PrintersForAnts/AntHead/UserMods/Wristwatch-BMG/CAD/AntHead WW-BMG - Tension Arm Assembly.step

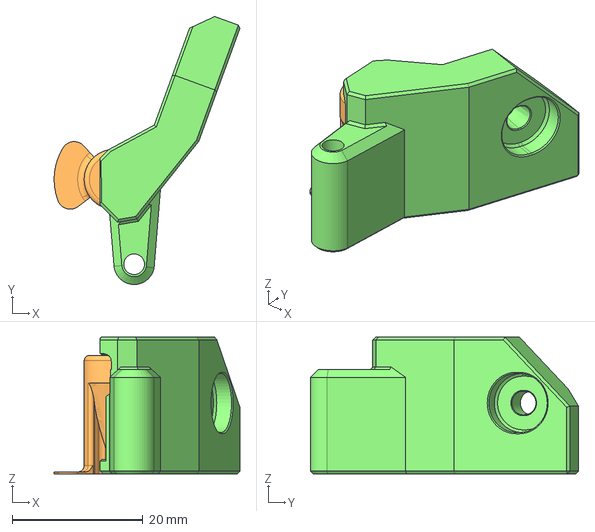
[picture p27: CAD file, 2025-04-11]
UserMods/Wristwatch-BMG/CAD/AntHead WW-BMG - Tension Arm Assembly.step
28.4 x 41.0 x 20.9 mm
WWBMG - Tension_Arm Support
AH WWBMG - Tension Arm
