PrintersForAnts/AntHead/UserMods/Papilio_Lite_Extruder_AntHead_Mod/STLs/AntHead_V43_Printed_Parts/LED_Logo_Assembly_x1.stl

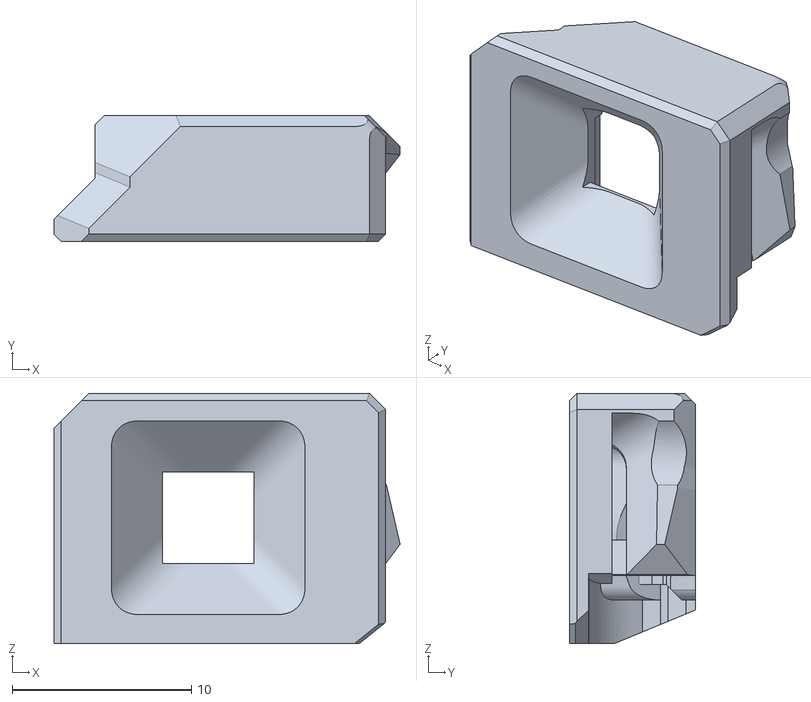
[picture p28: CAD file, 2025-02-15]
UserMods/Papilio_Lite_Extruder_AntHead_Mod/STLs/AntHead_V43_Printed_Parts/LED_Logo_Assembly_x1.stl
19.3 x 7.01 x 14.0
