PrintersForAnts/AntHead/Mini_AntHead/main_housing.stl

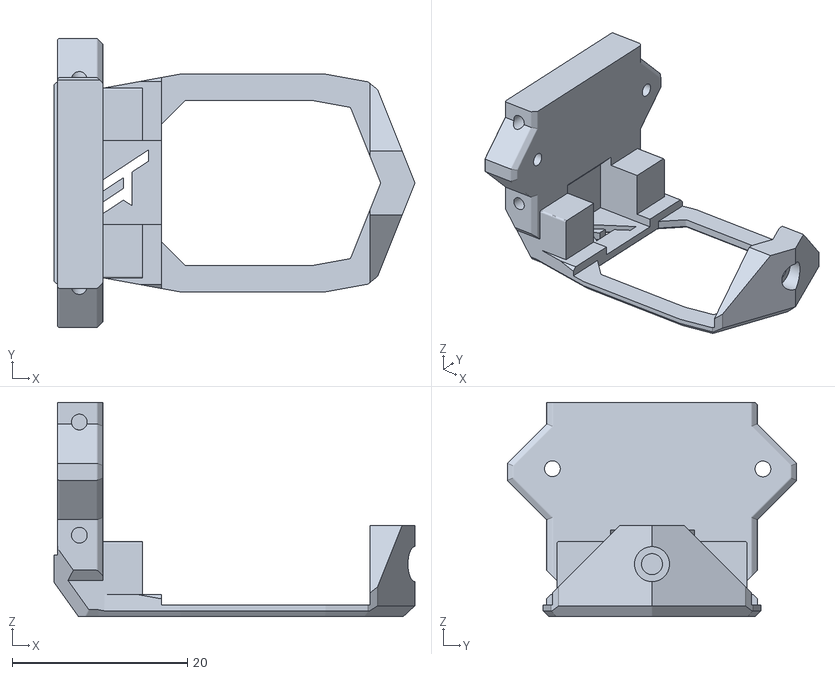
[picture p29: CAD file, 2025-01-11]
Mini_AntHead/main_housing.stl
41.2 x 33.0 x 24.4
