PrintersForAnts/AntHead/CAD/Base_CAD_Files/Anthead_Bowden.step

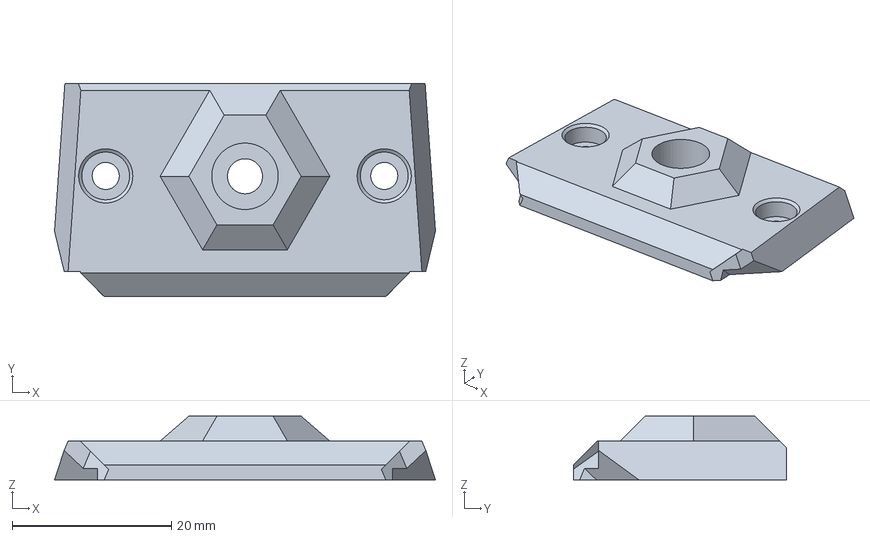
[picture p30: CAD file, 2025-11-22]
CAD/Base_CAD_Files/Anthead_Bowden.step
47.9 x 26.8 x 8.00 mm
