PrintersForAnts/AntHead/CAD/Extruders/NH36_Board_Cover.step

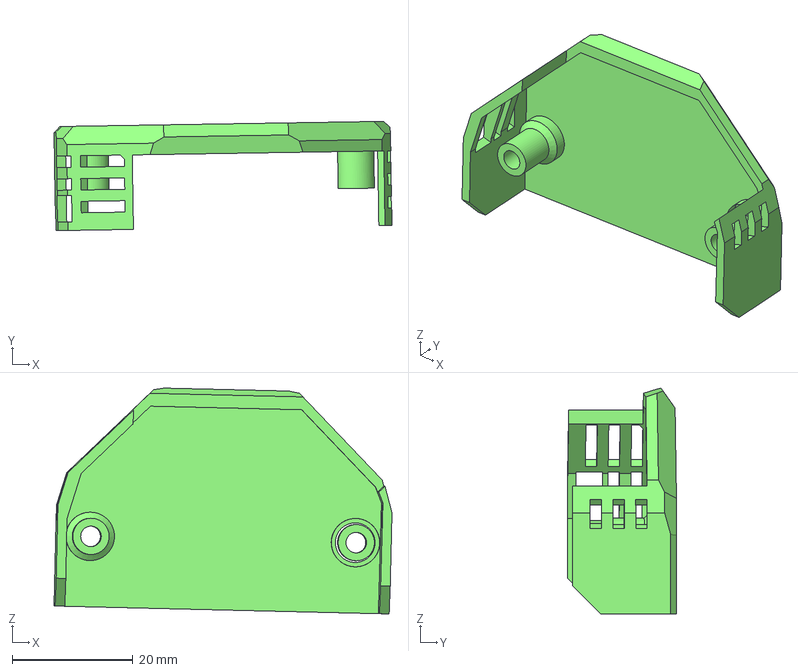
[picture p31: CAD file, 2025-07-28]
CAD/Extruders/NH36_Board_Cover.step
55.9 x 18.1 x 37.3 mm
