PrintersForAnts/AntHead/Mini_AntHead/[a]_logo_insert.stl

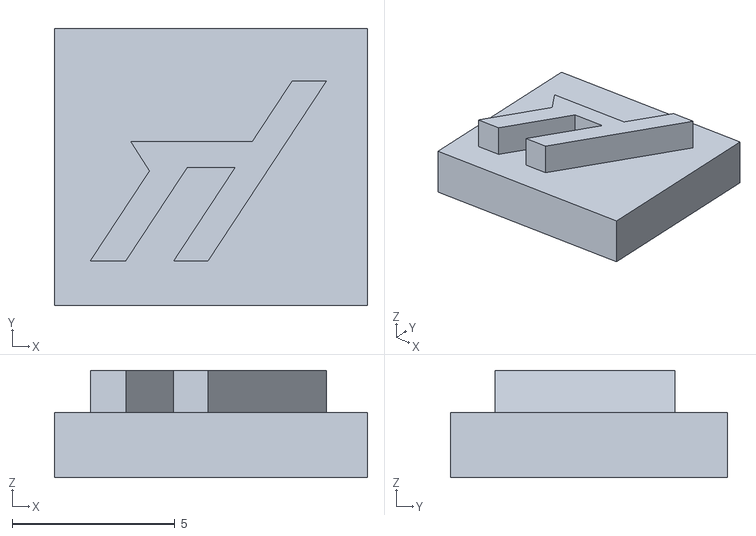
[picture p32: CAD file, 2025-01-11]
Mini_AntHead/[a]_logo_insert.stl
9.61 x 8.51 x 3.30
