PrintersForAnts/AntHead/STLs/2020_Carriage/beacon_carto_uhf_x1.stl

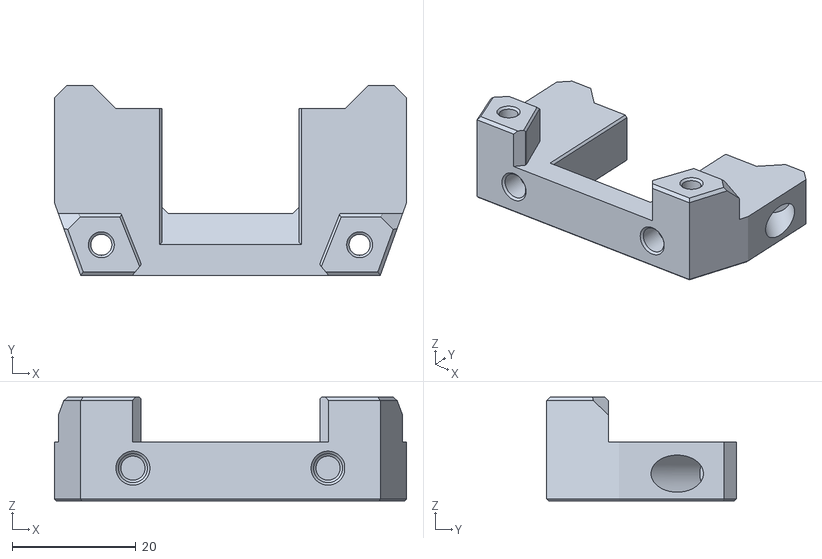
[picture p33: CAD file, 2025-08-02]
STLs/2020_Carriage/beacon_carto_uhf_x1.stl
57.0 x 30.7 x 16.8
