PrintersForAnts/AntHead/STLs/Ducts/HF/[a]_right_duct_hf_x1.stl

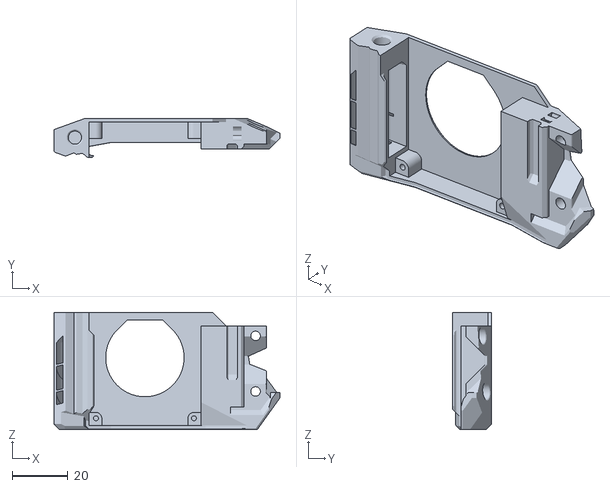
[picture p35: CAD file, 2025-07-28]
STLs/Ducts/HF/[a]_right_duct_hf_x1.stl
80.8 x 13.8 x 42.0
