PrintersForAnts/AntHead/STLs/Ducts/HF/Leaf_Cutter/[a]_left_duct_hf_hb92_lc_x1.stl

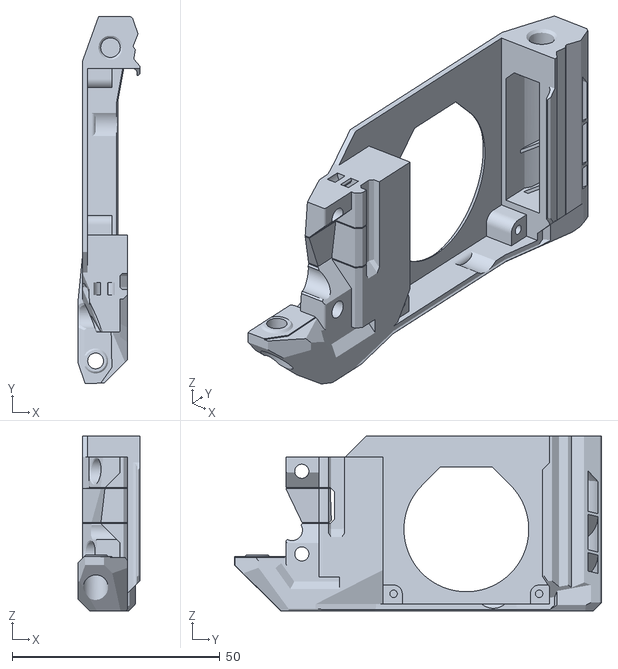
[picture p36: CAD file, 2025-07-28]
STLs/Ducts/HF/Leaf_Cutter/[a]_left_duct_hf_hb92_lc_x1.stl
14.8 x 88.2 x 42.0
