PrintersForAnts/AntHead/STLs/Ducts/SF/Leaf_Cutter/[a]_left_duct_lc_x1.stl

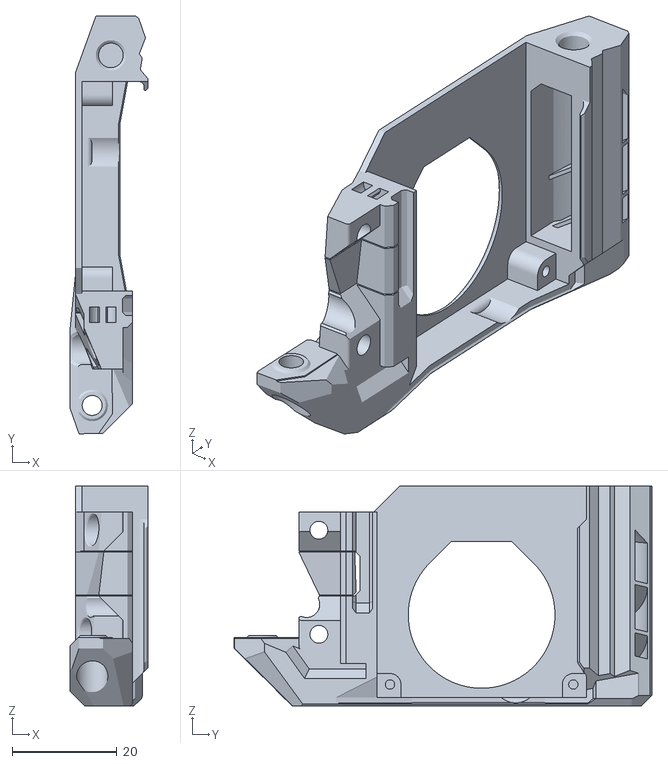
[picture p38: CAD file, 2025-07-28]
STLs/Ducts/SF/Leaf_Cutter/[a]_left_duct_lc_x1.stl
14.8 x 79.7 x 42.0
