PrintersForAnts/AntHead/STLs/Ducts/UHF/[a]_right_duct_uhf_x1.stl

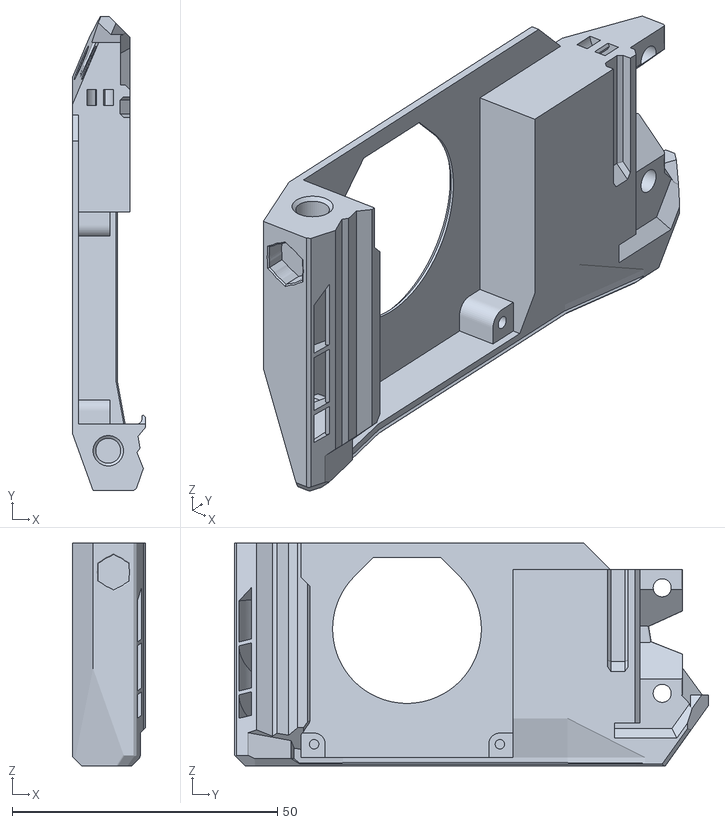
[picture p39: CAD file, 2025-07-28]
STLs/Ducts/UHF/[a]_right_duct_uhf_x1.stl
13.8 x 89.3 x 42.0
