PrintersForAnts/AntHead/STLs/Ducts/UHF/Leaf_Cutter/[a]_left_duct_uhf_lc_x1.stl

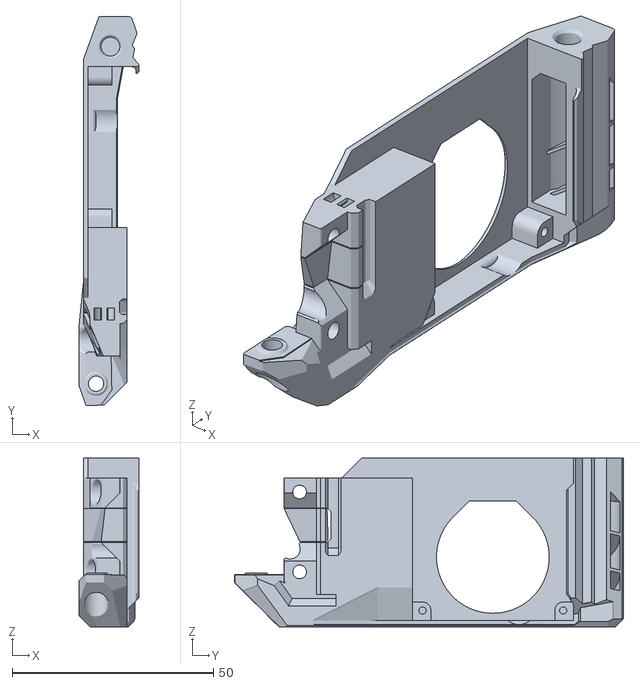
[picture p40: CAD file, 2025-07-28]
STLs/Ducts/UHF/Leaf_Cutter/[a]_left_duct_uhf_lc_x1.stl
14.8 x 96.7 x 42.0
