PrintersForAnts/AntHead/STLs/Extruders/BMG/BoardMounts/toolhead_board_mount_anthead_bmg_micron.stl

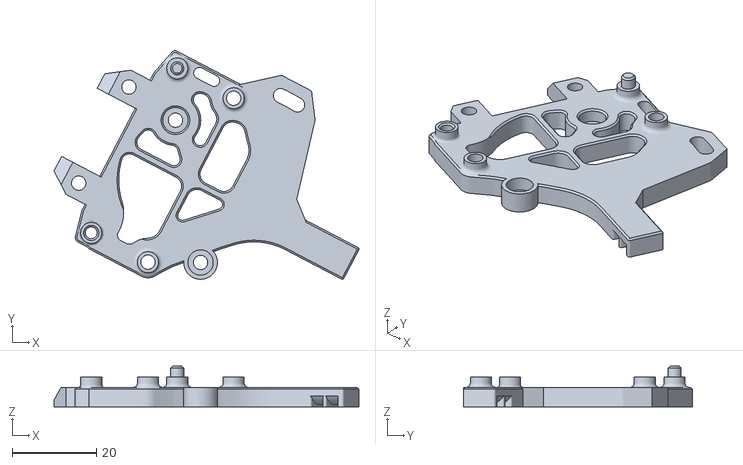
[picture p41: CAD file, 2025-07-28]
STLs/Extruders/BMG/BoardMounts/toolhead_board_mount_anthead_bmg_micron.stl
72.3 x 54.2 x 9.60
