PrintersForAnts/AntHead/STLs/Extruders/BMG/tensioner_arm_b_x1.stl

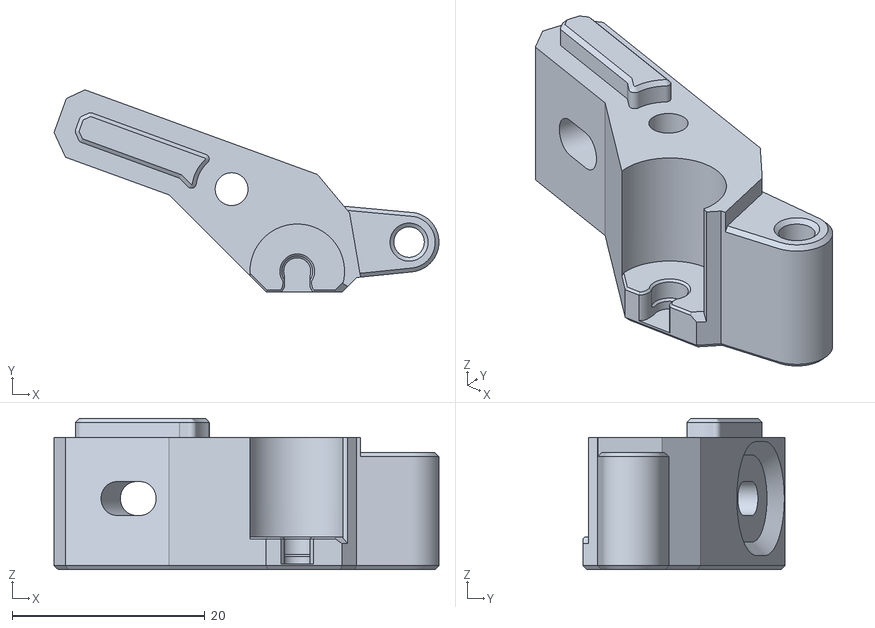
[picture p42: CAD file, 2024-10-09]
STLs/Extruders/BMG/tensioner_arm_b_x1.stl
39.9 x 21.0 x 15.7
