PrintersForAnts/AntHead/STLs/Extruders/G2/Board Mounts/toolhead_board_mount_anthead_G2_micron.stl

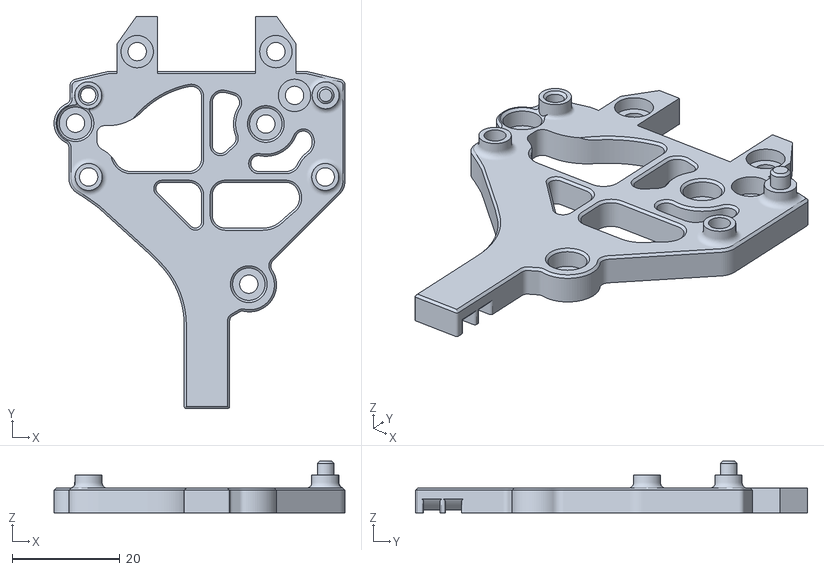
[picture p43: CAD file, 2025-07-28]
STLs/Extruders/G2/Board Mounts/toolhead_board_mount_anthead_G2_micron.stl
53.9 x 72.7 x 9.60
