PrintersForAnts/AntHead/STLs/Extruders/G2/pug_mount_a_x1.stl

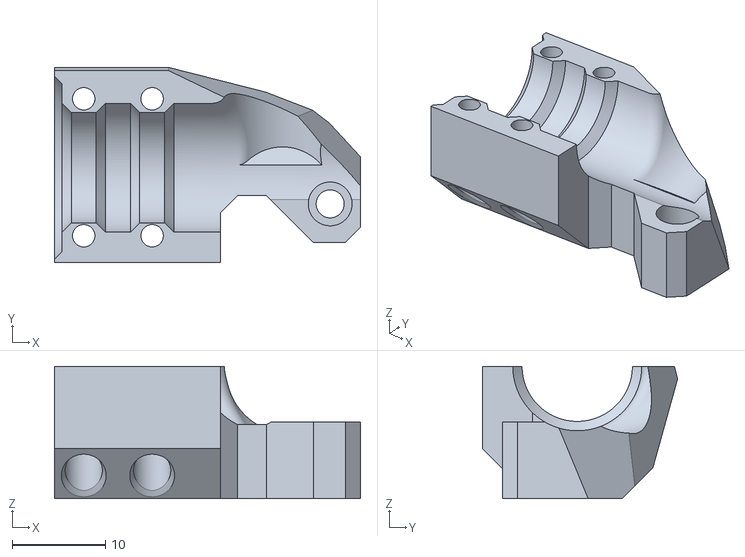
[picture p44: CAD file, 2025-10-02]
STLs/Extruders/G2/pug_mount_a_x1.stl
32.8 x 20.9 x 14.2
