PrintersForAnts/AntHead/STLs/Grills/[a]_hex_grill_x1.stl

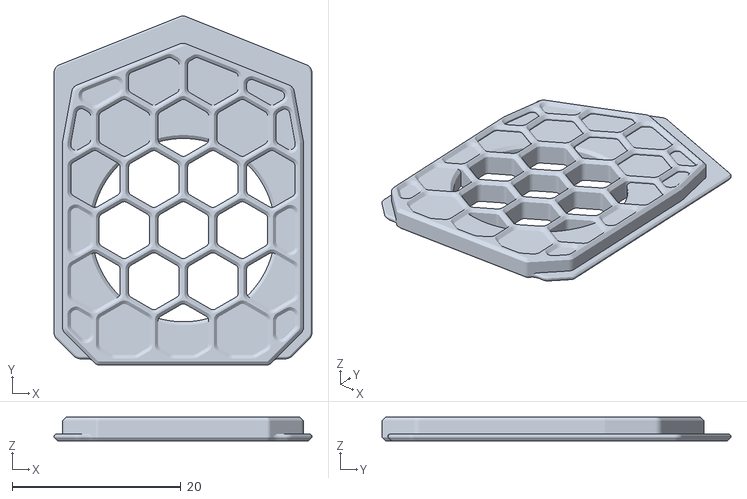
[picture p45: CAD file, 2026-03-18]
STLs/Grills/[a]_hex_grill_x1.stl
30.6 x 41.4 x 2.80
