PrintersForAnts/AntHead/STLs/Hotends/[a]_rapido_x_m2.5_x1.stl

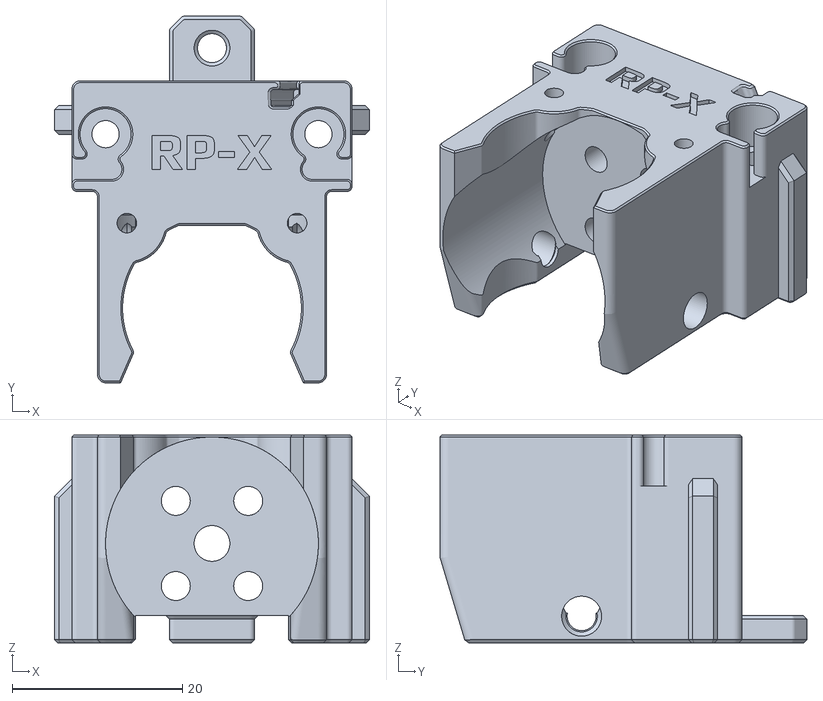
[picture p46: CAD file, 2026-10-05]
STLs/Hotends/[a]_rapido_x_m2.5_x1.stl
37.0 x 43.1 x 24.4
