PrintersForAnts/AntHead/STLs/LeafCutter/[a]_26mm_blade_holder_x1.stl

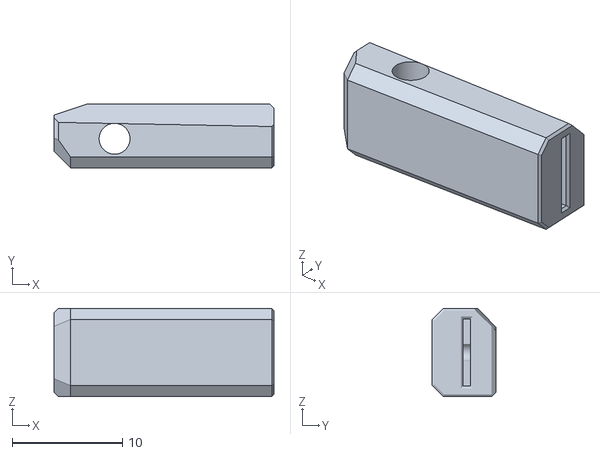
[picture p47: CAD file, 2025-07-28]
STLs/LeafCutter/[a]_26mm_blade_holder_x1.stl
20.0 x 5.80 x 8.00
