PrintersForAnts/AntHead/STLs/LEDs/[o]_light_shield_stealth_fork_x1.stl

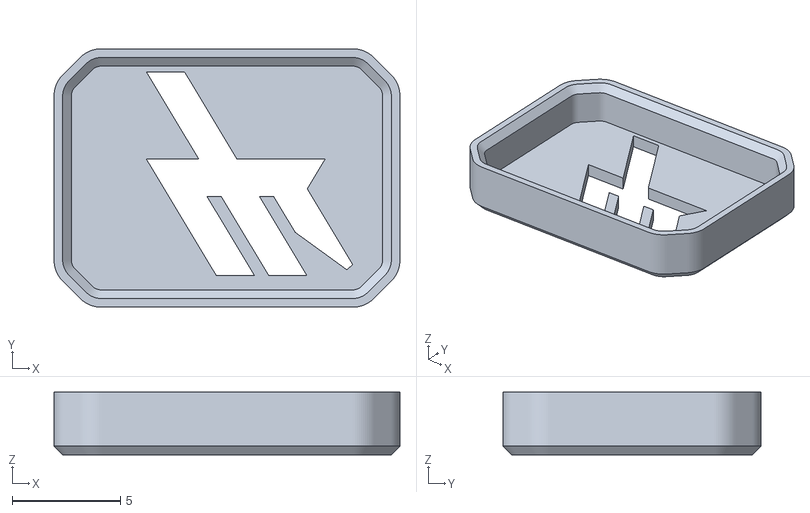
[picture p48: CAD file, 2025-05-28]
STLs/LEDs/[o]_light_shield_stealth_fork_x1.stl
16.0 x 11.9 x 2.90
