PrintersForAnts/AntHead/UserMods/hartk/crossbow/CAD/WWG2_Anthead_Crossbow_NoSensors.step

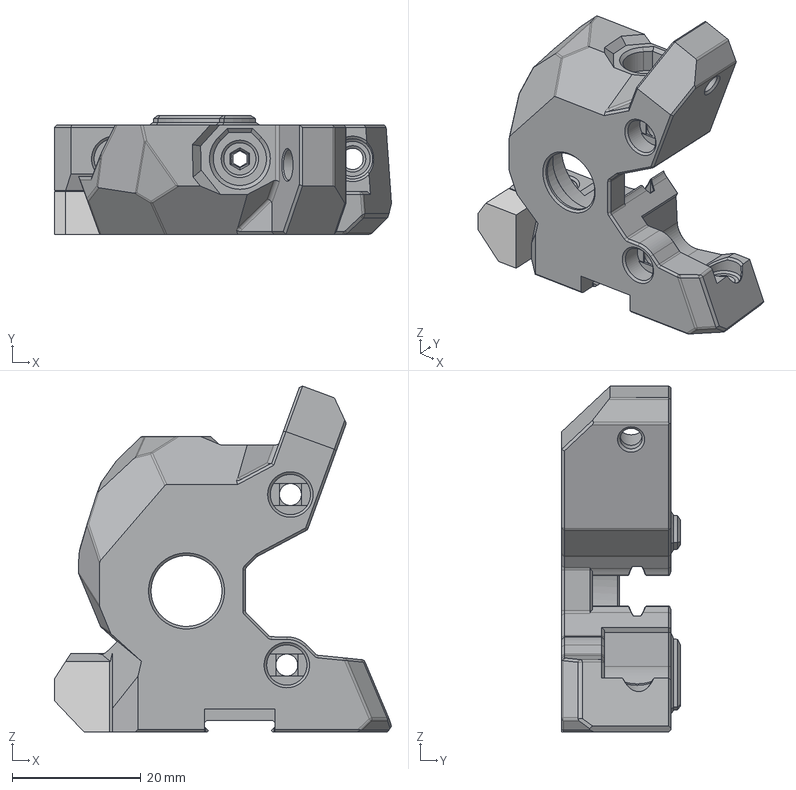
[picture p49: CAD file, 2026-05-15]
UserMods/hartk/crossbow/CAD/WWG2_Anthead_Crossbow_NoSensors.step
52.3 x 18.4 x 53.7 mm
