PrintersForAnts/AntHead/UserMods/hartk/crossbow/STLs/anthead_crossbow_mount.stl

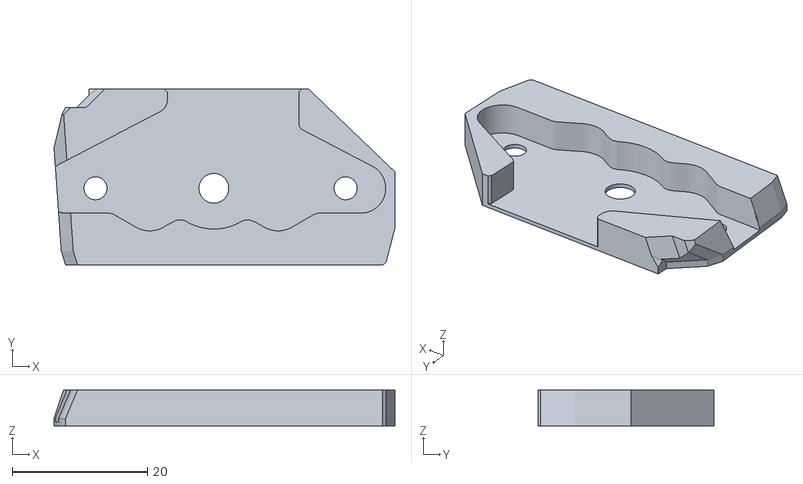
[picture p50: CAD file, 2025-11-22]
UserMods/hartk/crossbow/STLs/anthead_crossbow_mount.stl
50.4 x 26.1 x 5.30
