PrintersForAnts/AntHead/UserMods/hartk/crossbow/STLs/Ducts/HF/[a]_left_duct_hf_hb92_crossbow_x1.stl

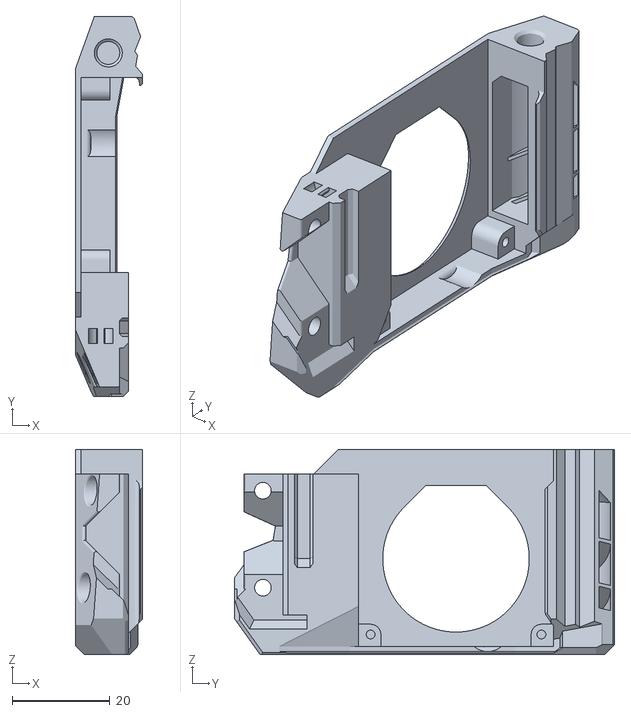
[picture p51: CAD file, 2025-11-22]
UserMods/hartk/crossbow/STLs/Ducts/HF/[a]_left_duct_hf_hb92_crossbow_x1.stl
13.8 x 77.9 x 42.0
