PrintersForAnts/AntHead/UserMods/hartk/crossbow/STLs/Ducts/SF/[a]_left_duct_crossbow_x1.stl

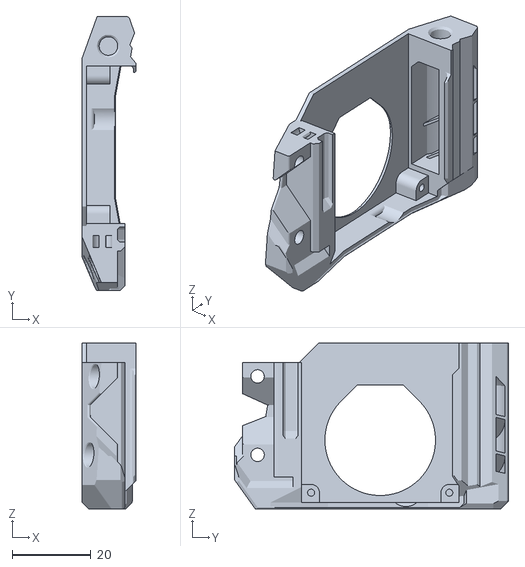
[picture p52: CAD file, 2025-11-22]
UserMods/hartk/crossbow/STLs/Ducts/SF/[a]_left_duct_crossbow_x1.stl
13.8 x 69.4 x 42.0
