PrintersForAnts/AntHead/UserMods/hartk/crossbow/STLs/WWG2/wwg2_front_body_no_sensors_x1.stl

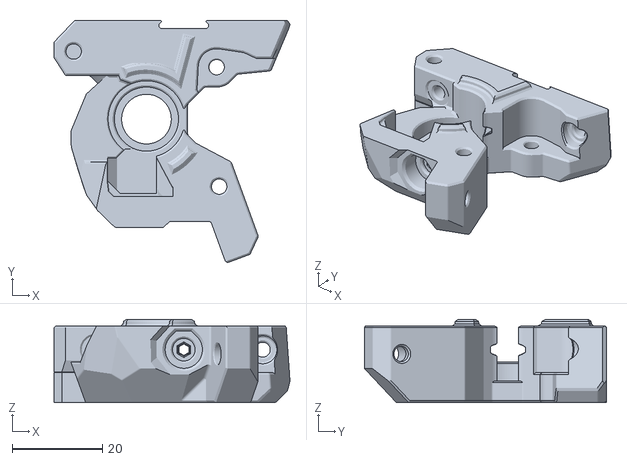
[picture p54: CAD file, 2026-05-15]
UserMods/hartk/crossbow/STLs/WWG2/wwg2_front_body_no_sensors_x1.stl
52.3 x 53.7 x 18.4
