PrintersForAnts/AntHead/UserMods/hartk/Trident_Umbilcal/Trident_Anthead_Umbilical v1.step

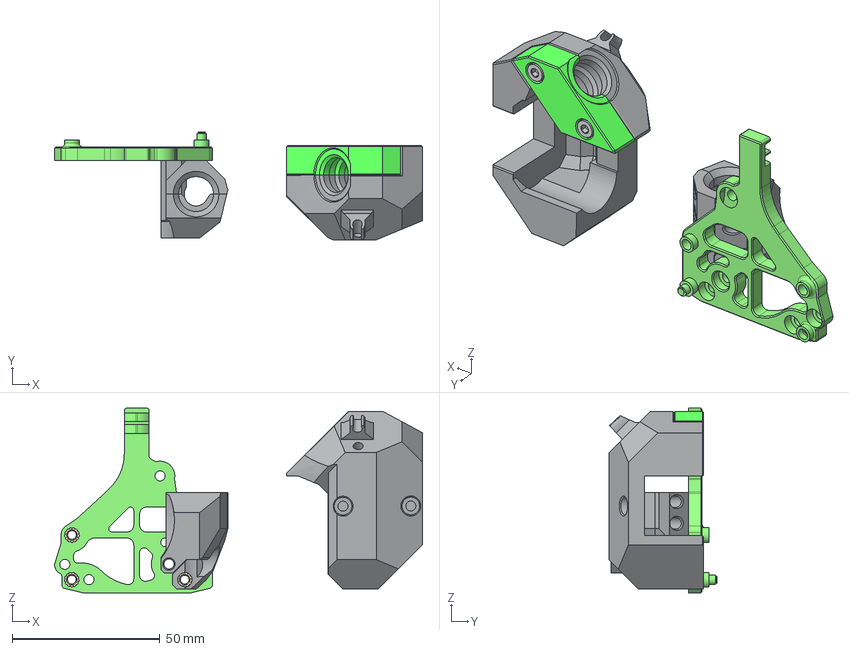
[picture p55: CAD file, 2025-02-18]
UserMods/hartk/Trident_Umbilcal/Trident_Anthead_Umbilical v1.step
124.6 x 36.5 x 62.5 mm
Printed_Spacer
NH36_1.4_MainMount
ToolheadPUG
Trident_Umbilical_PUG_Cover
Trident_Umbilical_PUG
M3 Threaded Insert x 6
M2x10 STS x 4
M3x8 SHCS x 2
