PrintersForAnts/AntHead/UserMods/Klicky Duct (Right)/Anthead_Right_Duct_Klicky Mount.STEP

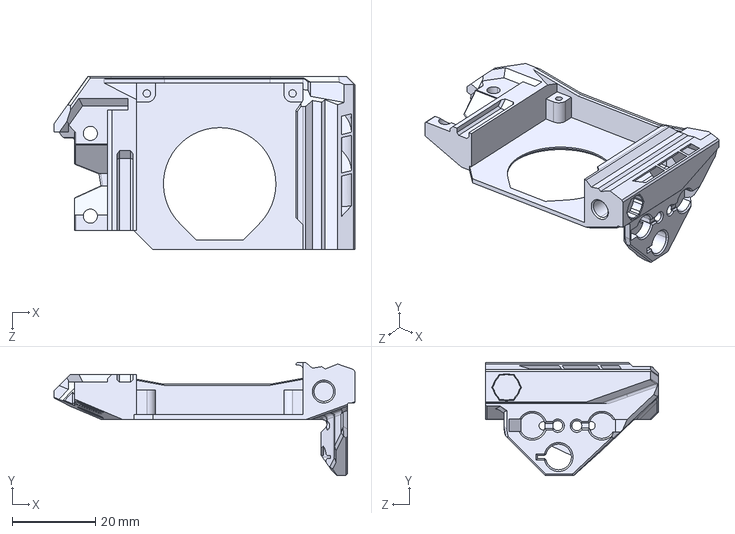
[picture p56: CAD file, 2025-03-16]
UserMods/Klicky Duct (Right)/Anthead_Right_Duct_Klicky Mount.STEP
72.3 x 27.3 x 41.6 mm
