PrintersForAnts/AntHead/UserMods/LED_Solder_Fixture/CAD/AntHead LED Fixture v4.step

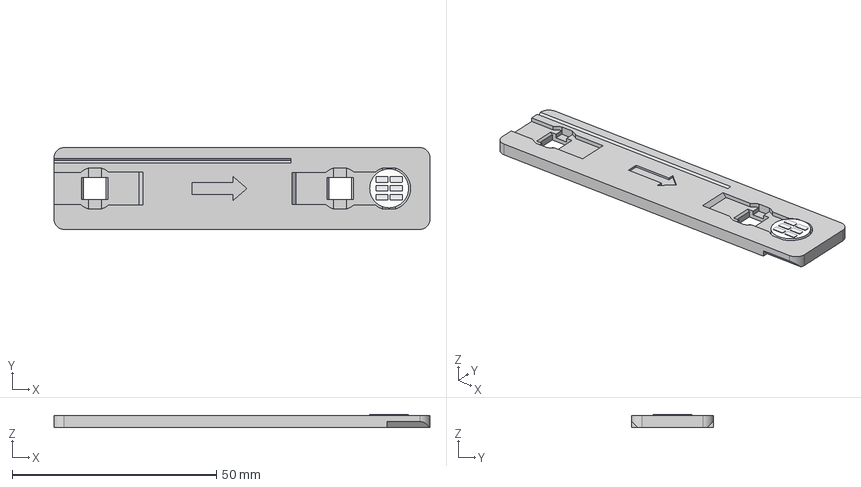
[picture p57: CAD file, 2025-02-27]
UserMods/LED_Solder_Fixture/CAD/AntHead LED Fixture v4.step
92.0 x 20.0 x 3.30 mm
