PrintersForAnts/AntHead/UserMods/LED_Solder_Fixture/STLs/AntHead LED Fixture Clamp.stl

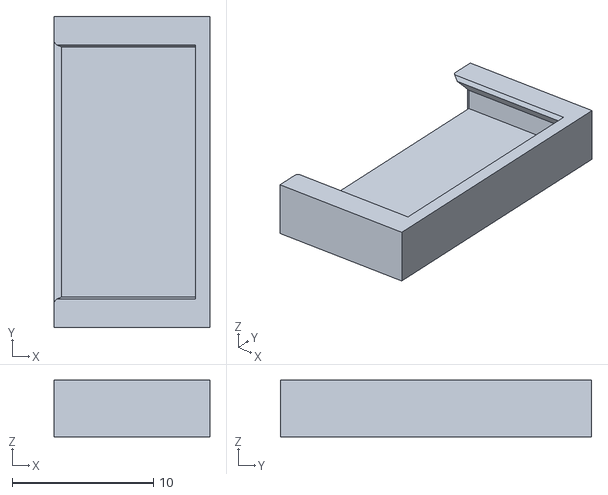
[picture p58: CAD file, 2025-02-27]
UserMods/LED_Solder_Fixture/STLs/AntHead LED Fixture Clamp.stl
11.0 x 22.0 x 4.00
