PrintersForAnts/AntHead/UserMods/Papilio_Lite_Extruder_AntHead_Mod/STLs/AntHead_V43_Printed_Parts/[a[_Left_Ducts_x1.stl

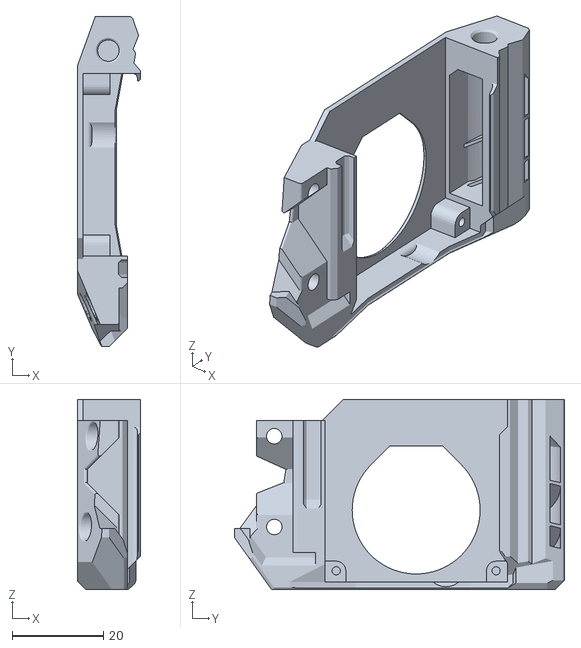
[picture p60: CAD file, 2025-02-21]
UserMods/Papilio_Lite_Extruder_AntHead_Mod/STLs/AntHead_V43_Printed_Parts/[a[_Left_Ducts_x1.stl
13.8 x 72.3 x 41.6
