PrintersForAnts/AntHead/UserMods/Papilio_Lite_Extruder_AntHead_Mod/STLs/AntPap_Printed_Parts/Common_parts/[clear]_AntPap_KevinAkaSam-Logo-AntPap_x1.stl

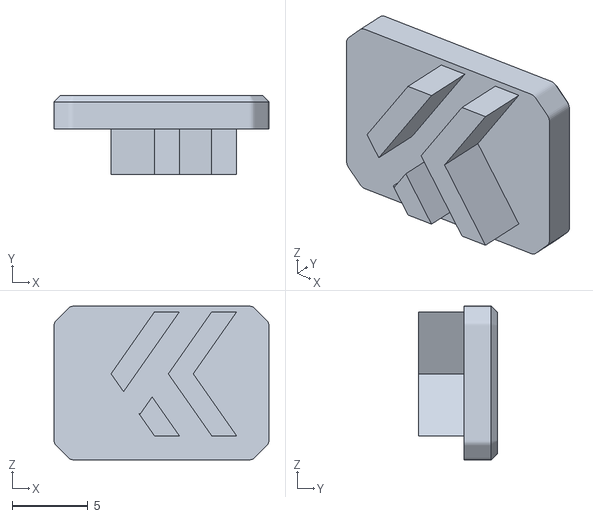
[picture p61: CAD file, 2025-02-21]
UserMods/Papilio_Lite_Extruder_AntHead_Mod/STLs/AntPap_Printed_Parts/Common_parts/[clear]_AntPap_KevinAkaSam-Logo-AntPap_x1.stl
14.2 x 5.19 x 10.1
