PrintersForAnts/AntHead/UserMods/Papilio_Lite_Extruder_AntHead_Mod/STLs/AntPap_Printed_Parts/Leafcutter-Runout_version/AntPap_Lever_x1.stl

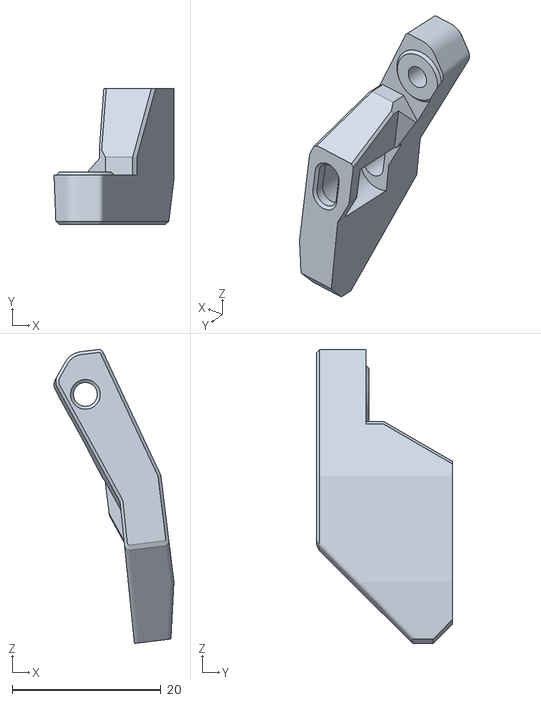
[picture p62: CAD file, 2025-02-21]
UserMods/Papilio_Lite_Extruder_AntHead_Mod/STLs/AntPap_Printed_Parts/Leafcutter-Runout_version/AntPap_Lever_x1.stl
16.1 x 18.2 x 39.5
