PrintersForAnts/AntHead/UserMods/Papilio_Lite_Extruder_AntHead_Mod/STLs/AntPap_Printed_Parts/Runout_version/RunOut_Pin_Opt1_AIORunout-pin.stl

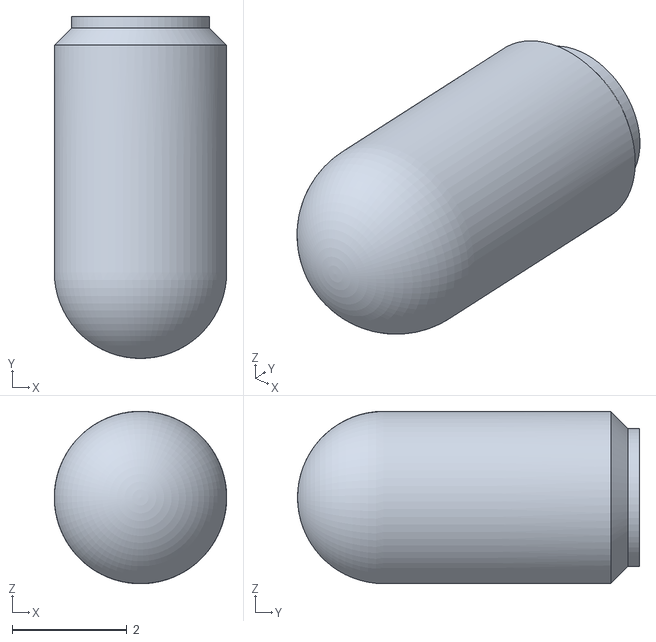
[picture p63: CAD file, 2025-02-21]
UserMods/Papilio_Lite_Extruder_AntHead_Mod/STLs/AntPap_Printed_Parts/Runout_version/RunOut_Pin_Opt1_AIORunout-pin.stl
3.00 x 5.95 x 3.00
