PrintersForAnts/AntHead/UserMods/Papilio_Lite_Extruder_AntHead_Mod/STLs/AntPap_Printed_Parts/Standard_version/AntPap_BaseMid_HGXv1_x1.stl

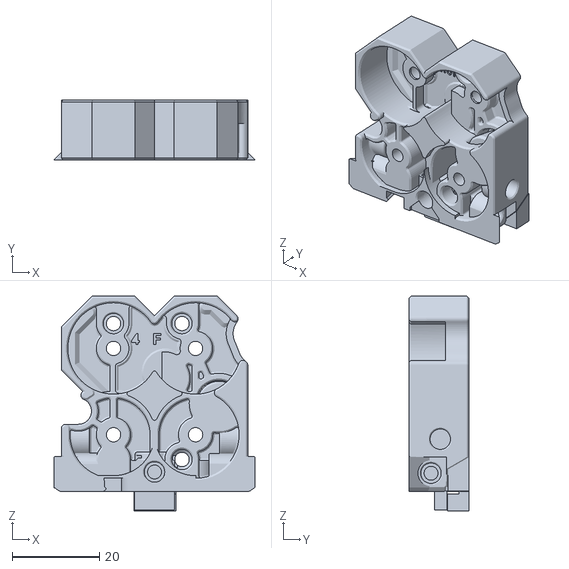
[picture p64: CAD file, 2025-02-21]
UserMods/Papilio_Lite_Extruder_AntHead_Mod/STLs/AntPap_Printed_Parts/Standard_version/AntPap_BaseMid_HGXv1_x1.stl
46.2 x 13.7 x 49.3
