PrintersForAnts/AntHead/UserMods/Papilio_Lite_Extruder_AntHead_Mod/STLs/Papilio_Lite_Parts/CutGuide_r2.stl

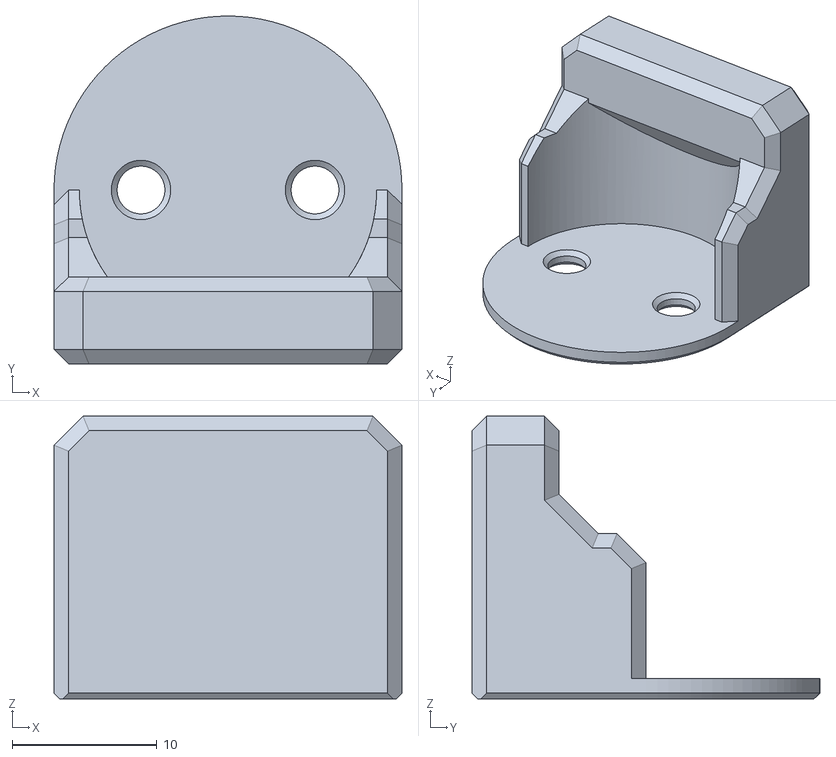
[picture p65: CAD file, 2025-02-21]
UserMods/Papilio_Lite_Extruder_AntHead_Mod/STLs/Papilio_Lite_Parts/CutGuide_r2.stl
24.0 x 24.0 x 19.5
