PrintersForAnts/AntHead/UserMods/SF_Nozzle_LEDs/CAD/Print_LED v1.step

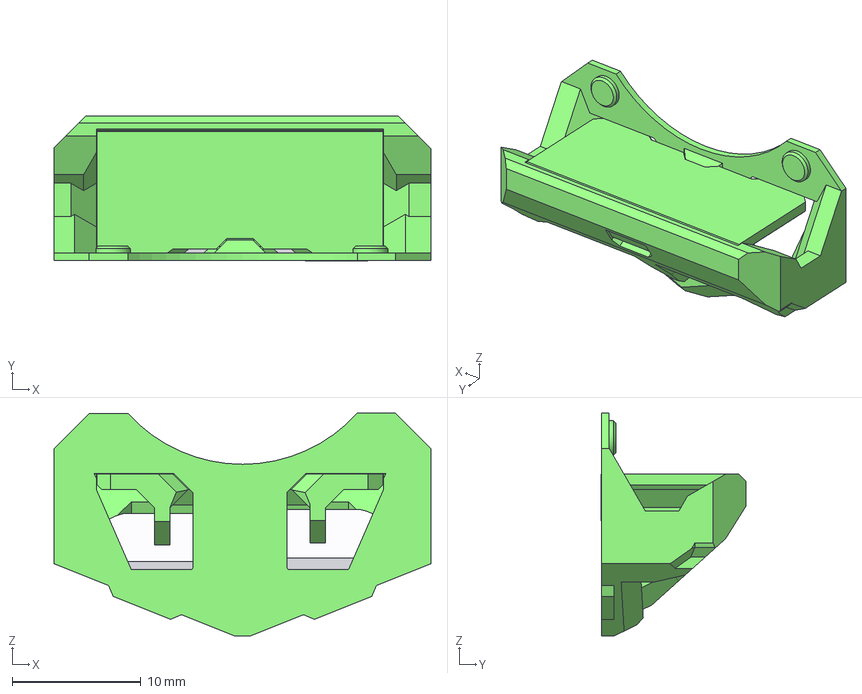
[picture p66: CAD file, 2025-04-11]
UserMods/SF_Nozzle_LEDs/CAD/Print_LED v1.step
29.3 x 11.2 x 17.3 mm
LED_Carrier
Restraint
WS2812B LED v1 x 2
