PrintersForAnts/AntHead/UserMods/SF_Nozzle_LEDs/STL/[a]_Nozzle_LED_Carrier.stl

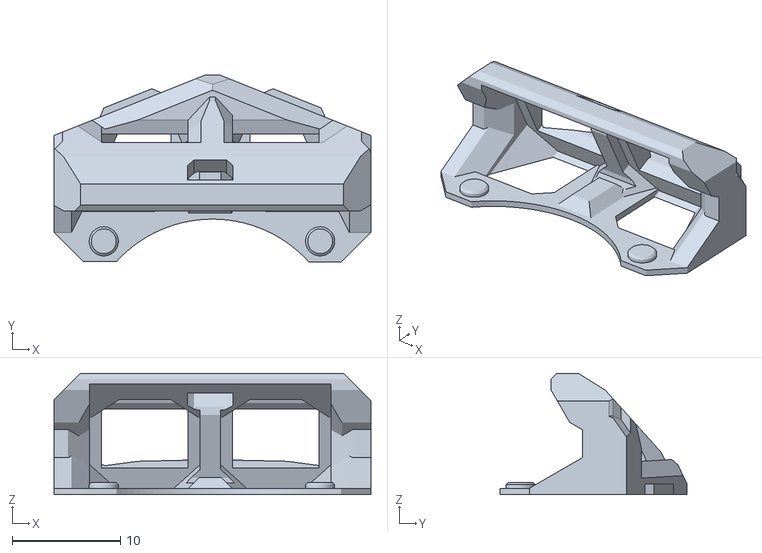
[picture p67: CAD file, 2025-04-11]
UserMods/SF_Nozzle_LEDs/STL/[a]_Nozzle_LED_Carrier.stl
29.3 x 17.3 x 11.2
