PrintersForAnts/AntHead/UserMods/ZeroClick_left_ducting/CAD/[a]_HX0_right_duct_standard_x1.stp

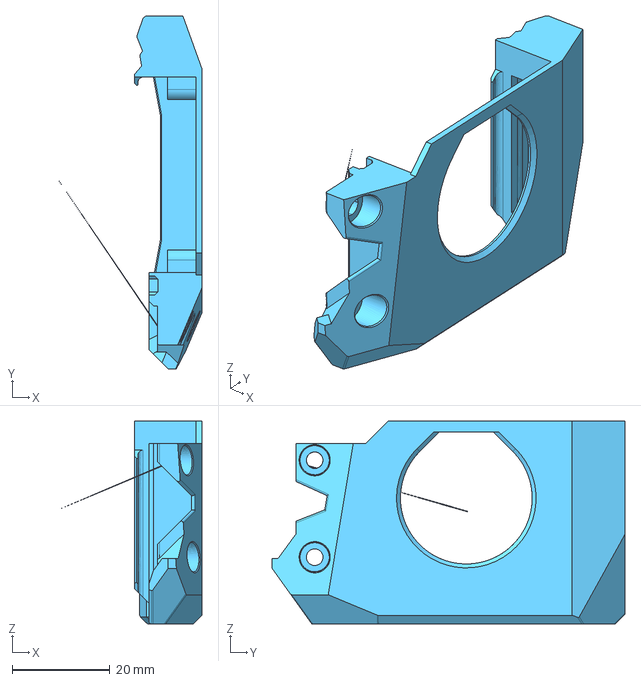
[picture p68: CAD file, 2024-12-16]
UserMods/ZeroClick_left_ducting/CAD/[a]_HX0_right_duct_standard_x1.stp
30.3 x 72.3 x 41.6 mm
