PrintersForAnts/AntHead/CAD/Base_CAD_Files/Hotend_Base v31.step

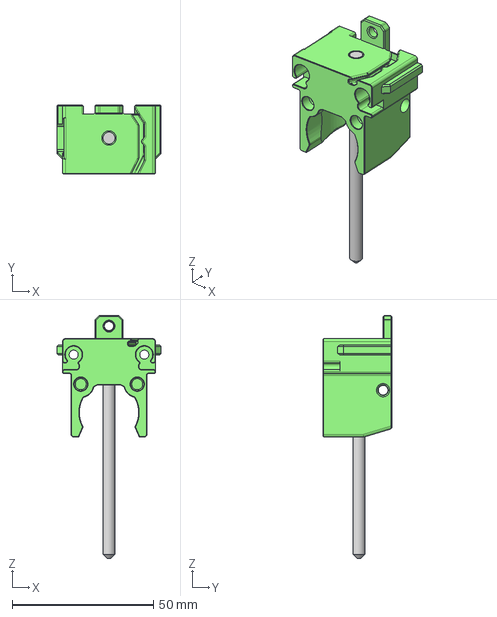
[picture p69: CAD file, 2025-07-28]
CAD/Base_CAD_Files/Hotend_Base v31.step
37.0 x 24.4 x 86.1 mm
