PrintersForAnts/AntHead/CAD/Extruders/LGX_Lite_Adapter.step

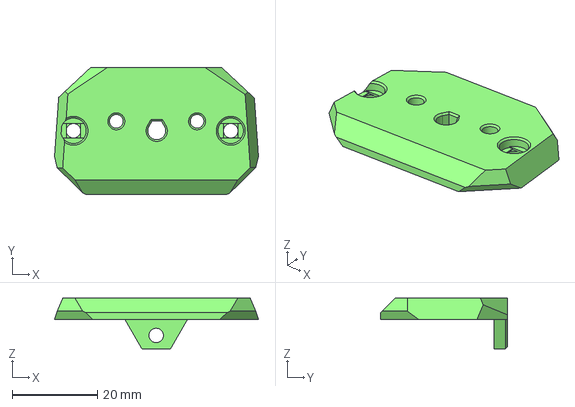
[picture p70: CAD file, 2024-10-18]
CAD/Extruders/LGX_Lite_Adapter.step
48.0 x 29.8 x 11.9 mm
