PrintersForAnts/AntHead/Mini_AntHead/[gray]_shaft.stl

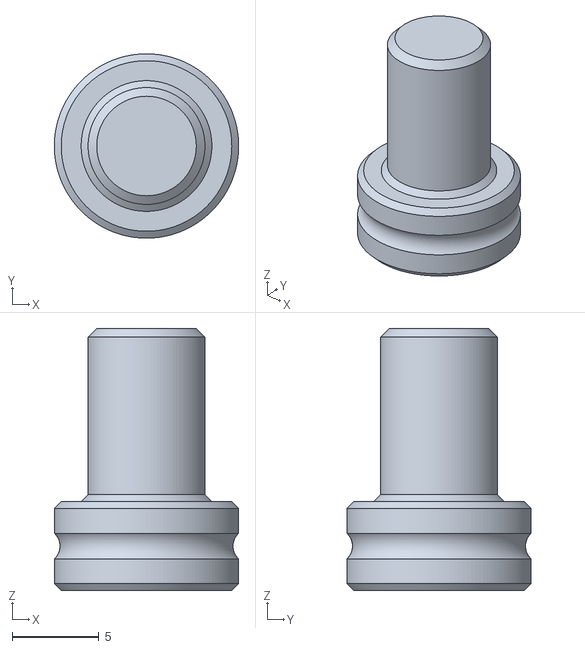
[picture p71: CAD file, 2025-01-11]
Mini_AntHead/[gray]_shaft.stl
10.6 x 10.6 x 15.1
