PrintersForAnts/AntHead/STLs/2020_Carriage/beacon_carto_hf_x1.stl

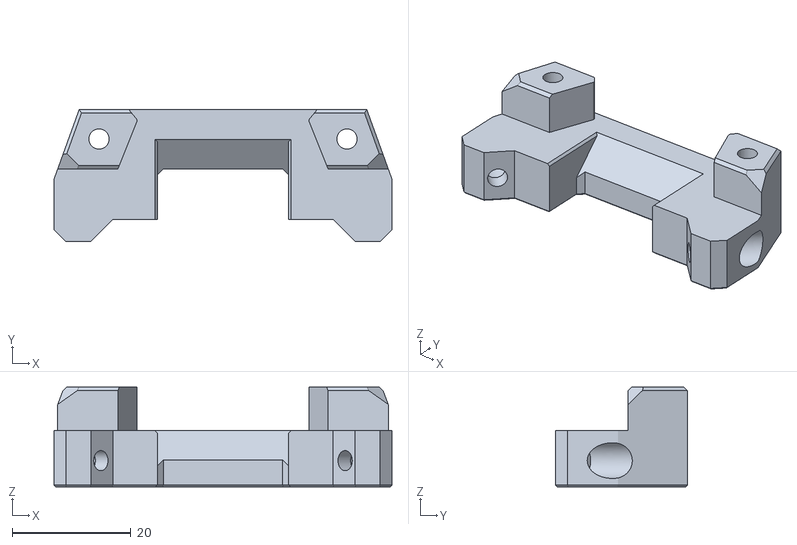
[picture p72: CAD file, 2025-08-02]
STLs/2020_Carriage/beacon_carto_hf_x1.stl
57.0 x 22.2 x 16.8
