PrintersForAnts/AntHead/STLs/2020_Carriage/Cartagrapher_CNC_Carriage_Adapter/UHF_CartoCNC_Anthead_Adapter.stl

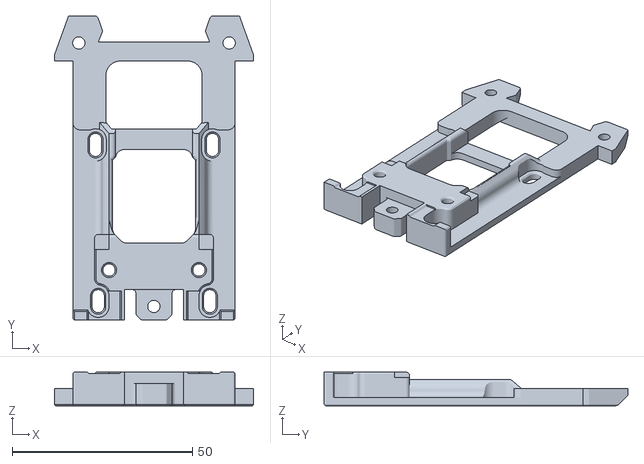
[picture p73: CAD file, 2025-02-11]
STLs/2020_Carriage/Cartagrapher_CNC_Carriage_Adapter/UHF_CartoCNC_Anthead_Adapter.stl
55.3 x 84.4 x 9.40
