PrintersForAnts/AntHead/STLs/Ducts/SF/[a]_right_duct_hb92_x1.stl

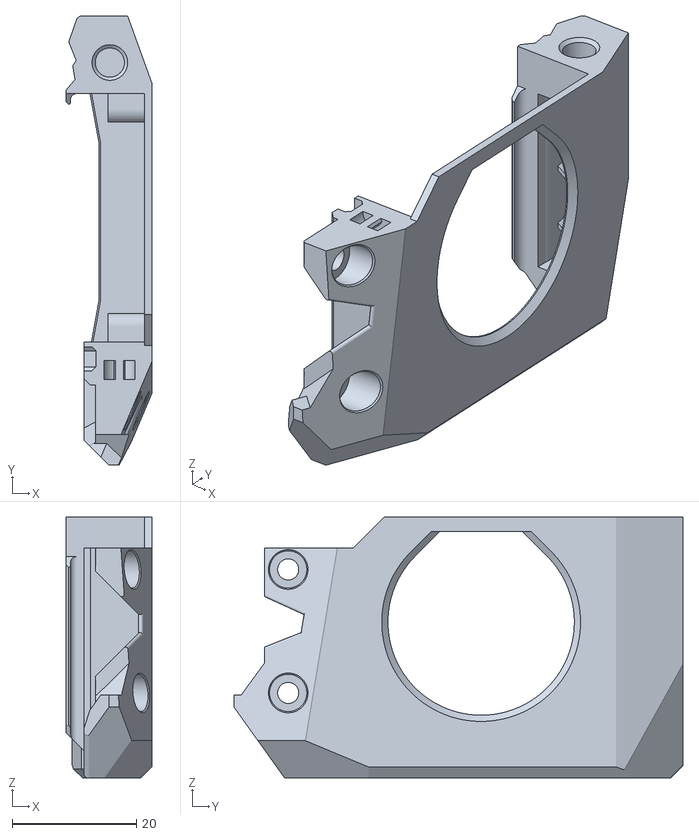
[picture p75: CAD file, 2025-07-28]
STLs/Ducts/SF/[a]_right_duct_hb92_x1.stl
13.8 x 72.3 x 42.0
