PrintersForAnts/AntHead/STLs/Extruders/BMG/BoardMounts/toolhead_board_mount_anthead_bmg_2020.stl

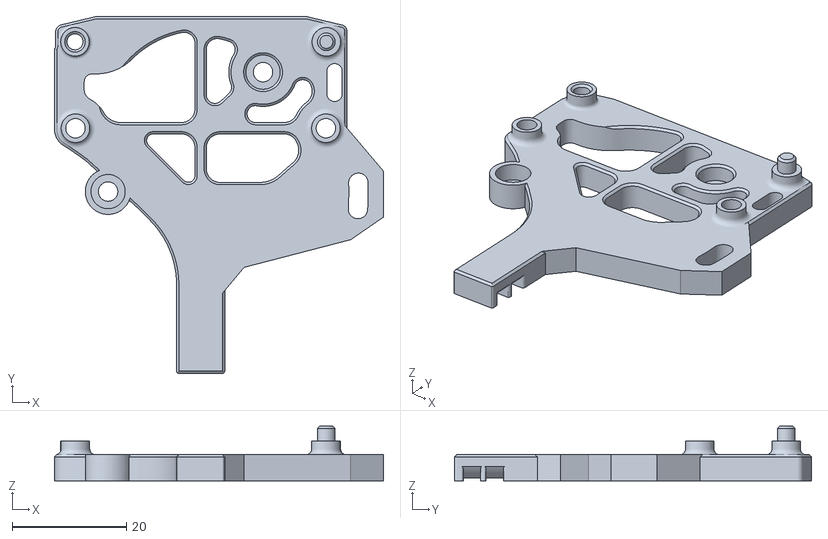
[picture p78: CAD file, 2025-07-28]
STLs/Extruders/BMG/BoardMounts/toolhead_board_mount_anthead_bmg_2020.stl
57.6 x 62.5 x 9.60
