PrintersForAnts/AntHead/STLs/Extruders/G2/Board Mounts/board_mount_spacer_micron.stl

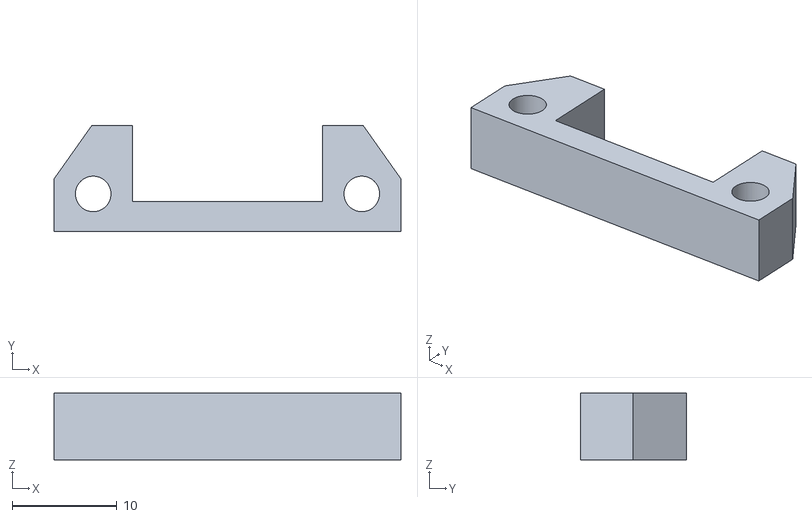
[picture p79: CAD file, 2025-07-28]
STLs/Extruders/G2/Board Mounts/board_mount_spacer_micron.stl
33.2 x 10.1 x 6.40
