PrintersForAnts/AntHead/STLs/Extruders/G2/pug_mount_b_x1.stl

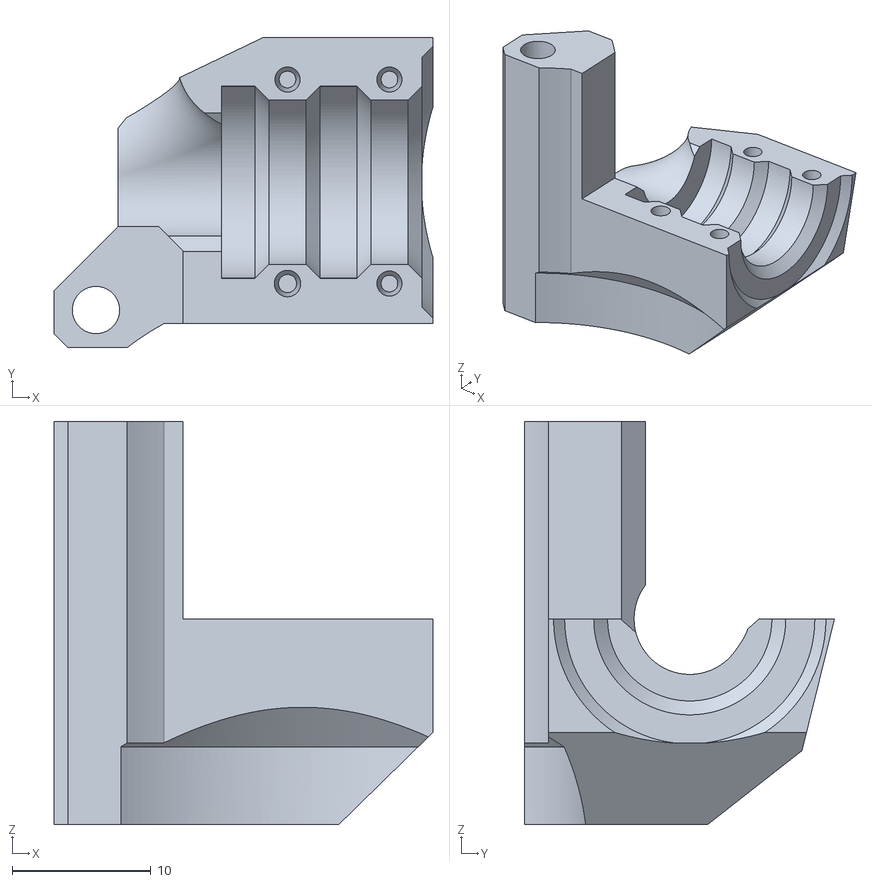
[picture p80: CAD file, 2025-10-02]
STLs/Extruders/G2/pug_mount_b_x1.stl
27.3 x 22.3 x 29.0
