PrintersForAnts/AntHead/STLs/LeafCutter/cutting_arm_x1.stl

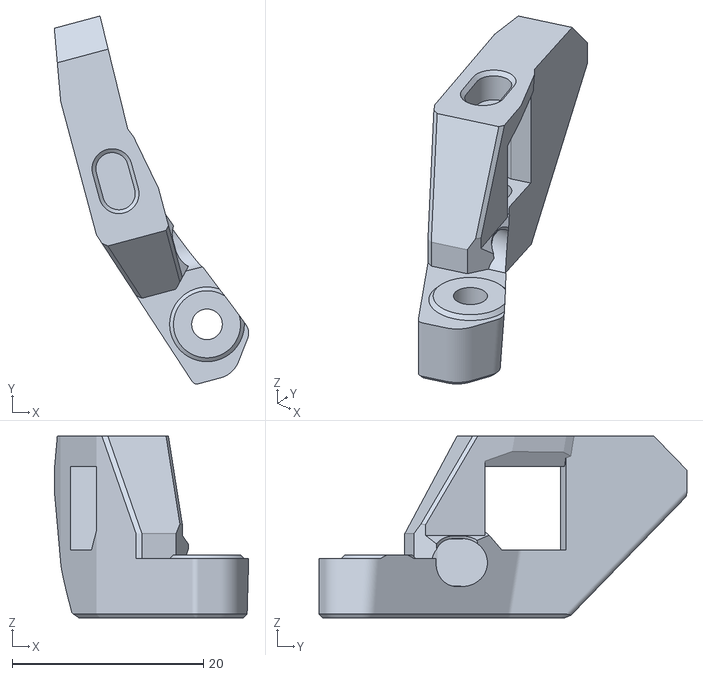
[picture p83: CAD file, 2025-07-28]
STLs/LeafCutter/cutting_arm_x1.stl
20.3 x 38.5 x 19.0
