PrintersForAnts/AntHead/STLs/LEDs/[c]_diffuser_stealth_fork_x1.stl

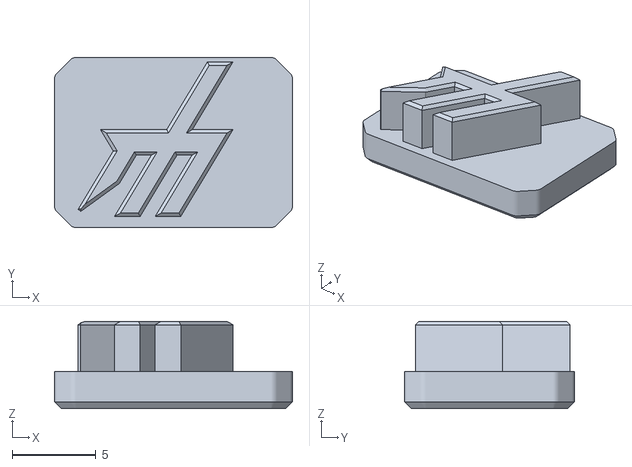
[picture p84: CAD file, 2025-05-28]
STLs/LEDs/[c]_diffuser_stealth_fork_x1.stl
14.2 x 10.1 x 5.20
