PrintersForAnts/AntHead/UserMods/hartk/crossbow/STLs/depressor_arm_base.stl

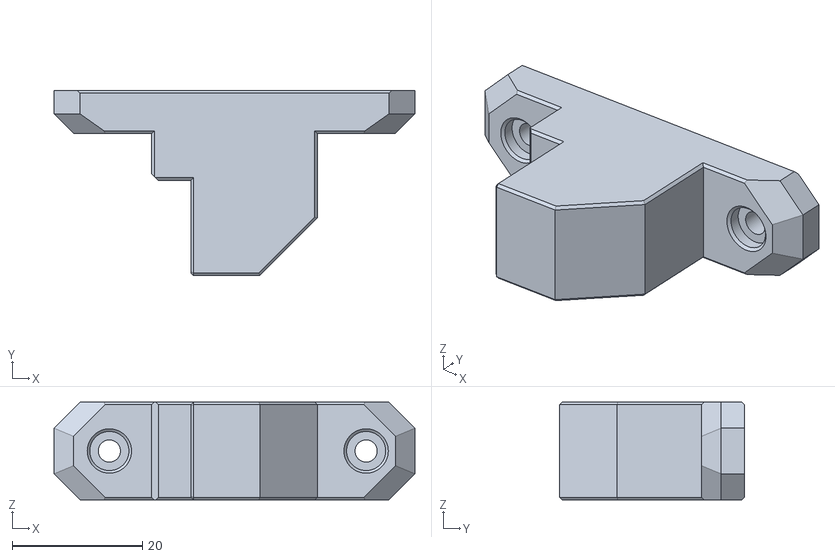
[picture p85: CAD file, 2025-11-22]
UserMods/hartk/crossbow/STLs/depressor_arm_base.stl
55.4 x 28.4 x 15.0
