PrintersForAnts/AntHead/UserMods/hartk/crossbow/STLs/Ducts/SF/[a]_left_duct_hb92_crossbow_x1.stl

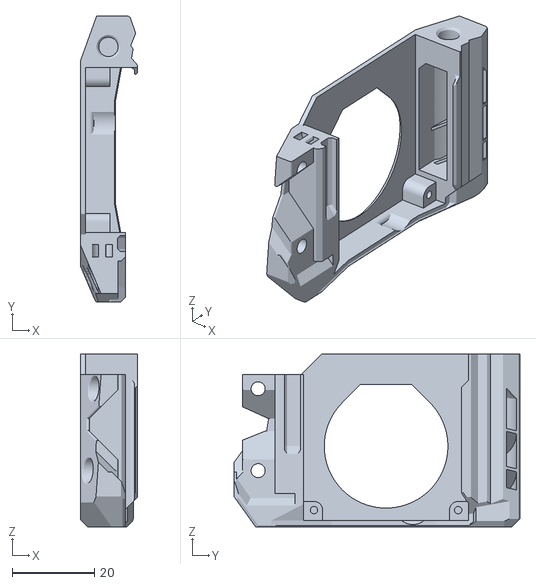
[picture p87: CAD file, 2025-11-22]
UserMods/hartk/crossbow/STLs/Ducts/SF/[a]_left_duct_hb92_crossbow_x1.stl
13.8 x 69.4 x 42.0
