PrintersForAnts/AntHead/UserMods/hartk/crossbow/STLs/Ducts/UHF/[a]_left_duct_uhf_crossbow_x1.stl

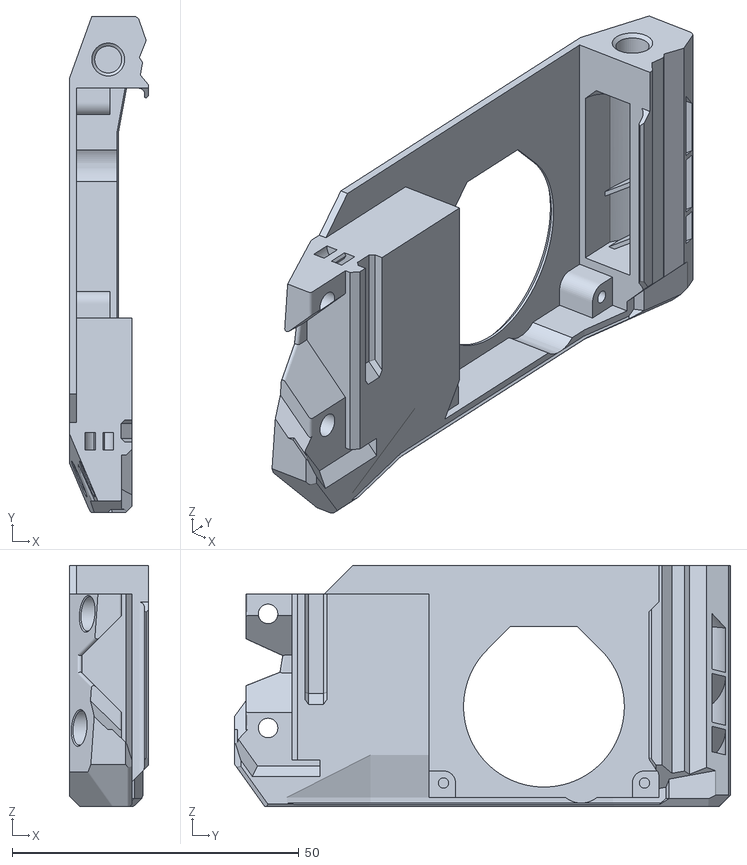
[picture p88: CAD file, 2025-11-22]
UserMods/hartk/crossbow/STLs/Ducts/UHF/[a]_left_duct_uhf_crossbow_x1.stl
13.8 x 86.4 x 42.0
