PrintersForAnts/AntHead/UserMods/hartk/crossbow/STLs/WWG2/[a]_wwg2_rear_body_x1.stl

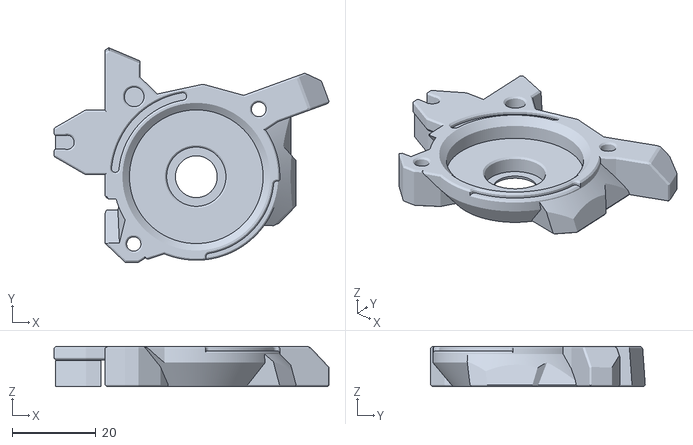
[picture p89: CAD file, 2025-11-22]
UserMods/hartk/crossbow/STLs/WWG2/[a]_wwg2_rear_body_x1.stl
65.9 x 51.4 x 9.60
