PrintersForAnts/AntHead/UserMods/LED_Solder_Fixture/STLs/AntHead LED Fixture.stl

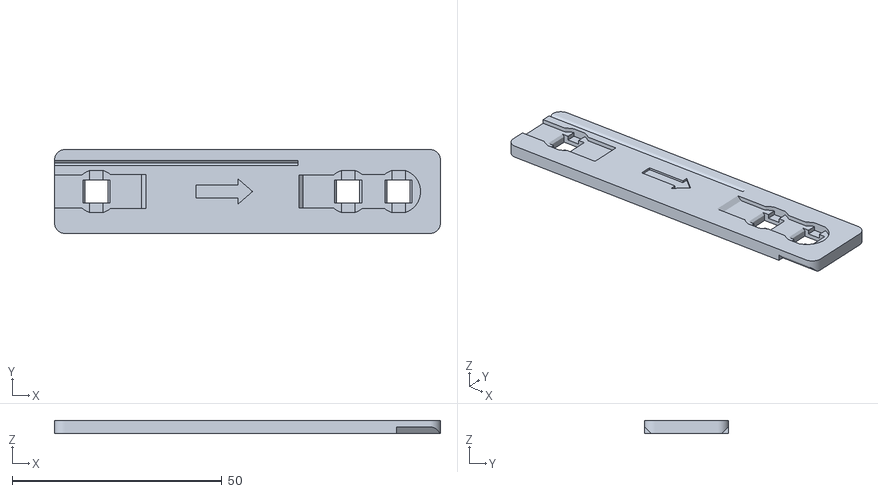
[picture p90: CAD file, 2025-02-27]
UserMods/LED_Solder_Fixture/STLs/AntHead LED Fixture.stl
92.0 x 20.0 x 3.00
